FabLabCordoba/matrizInyeccionCOVID19/img/Molde0.jpeg

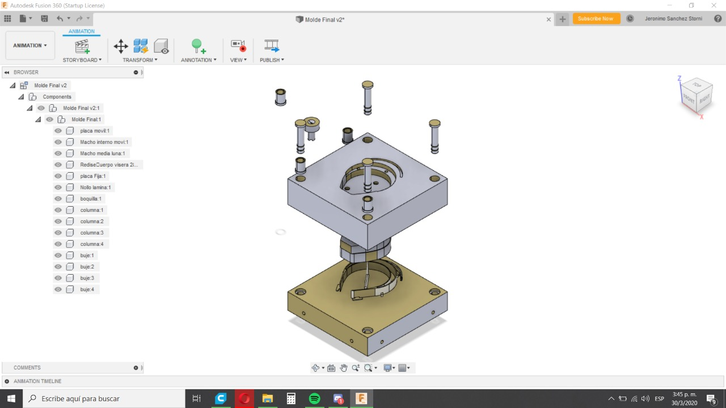
img/Molde0.jpeg
