FabLabCordoba/matrizInyeccionCOVID19/img/Molde2.jpeg

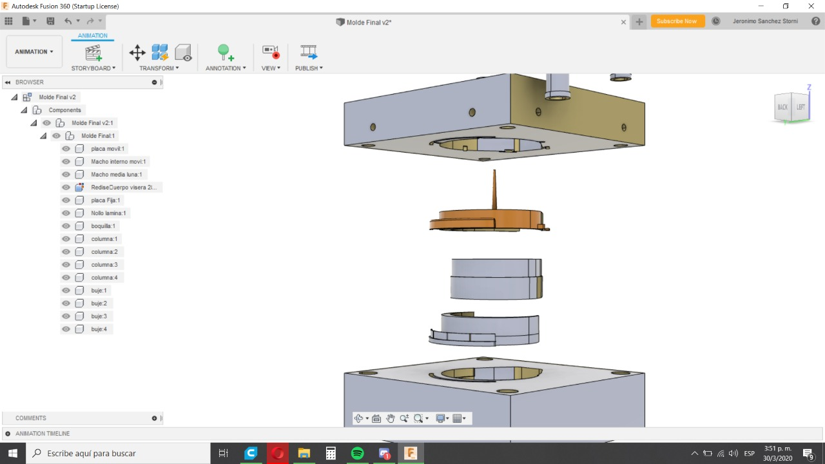
img/Molde2.jpeg
